ahmadalkawasmeh/HydraSmart/application preview/ecPage.png

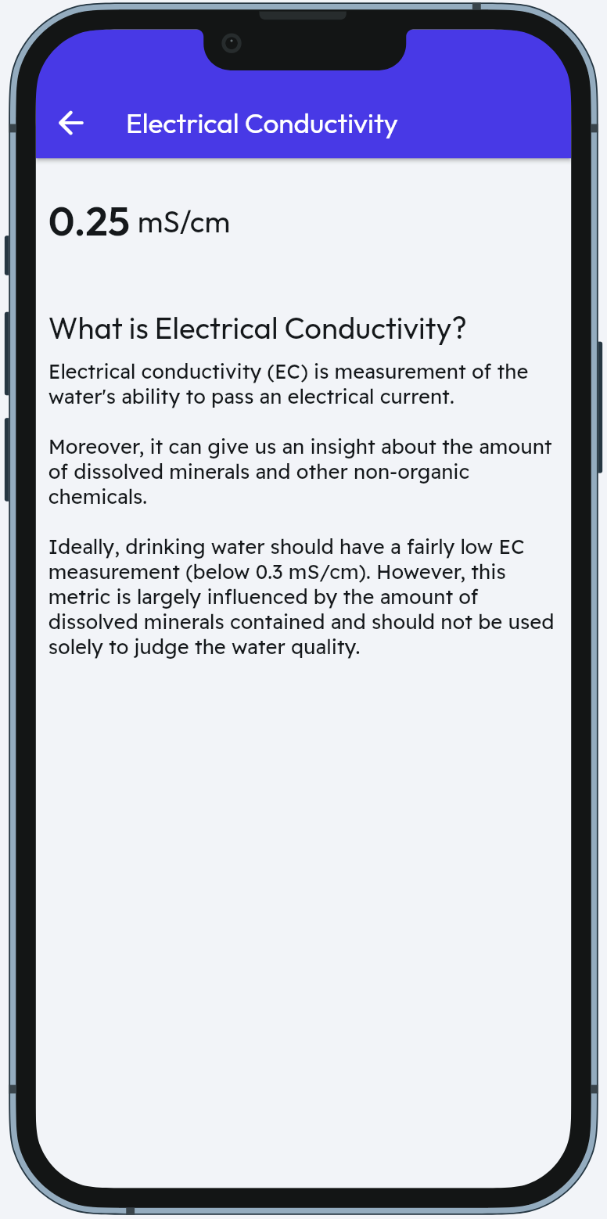
application preview/ecPage.png
