ahmadalkawasmeh/HydraSmart/application preview/homePage.png

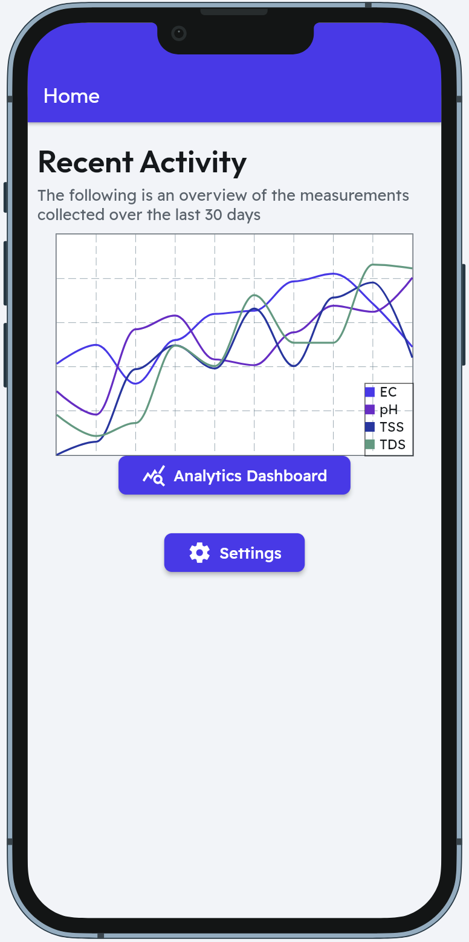
application preview/homePage.png
