ahmadalkawasmeh/HydraSmart/application preview/tdsPage.png

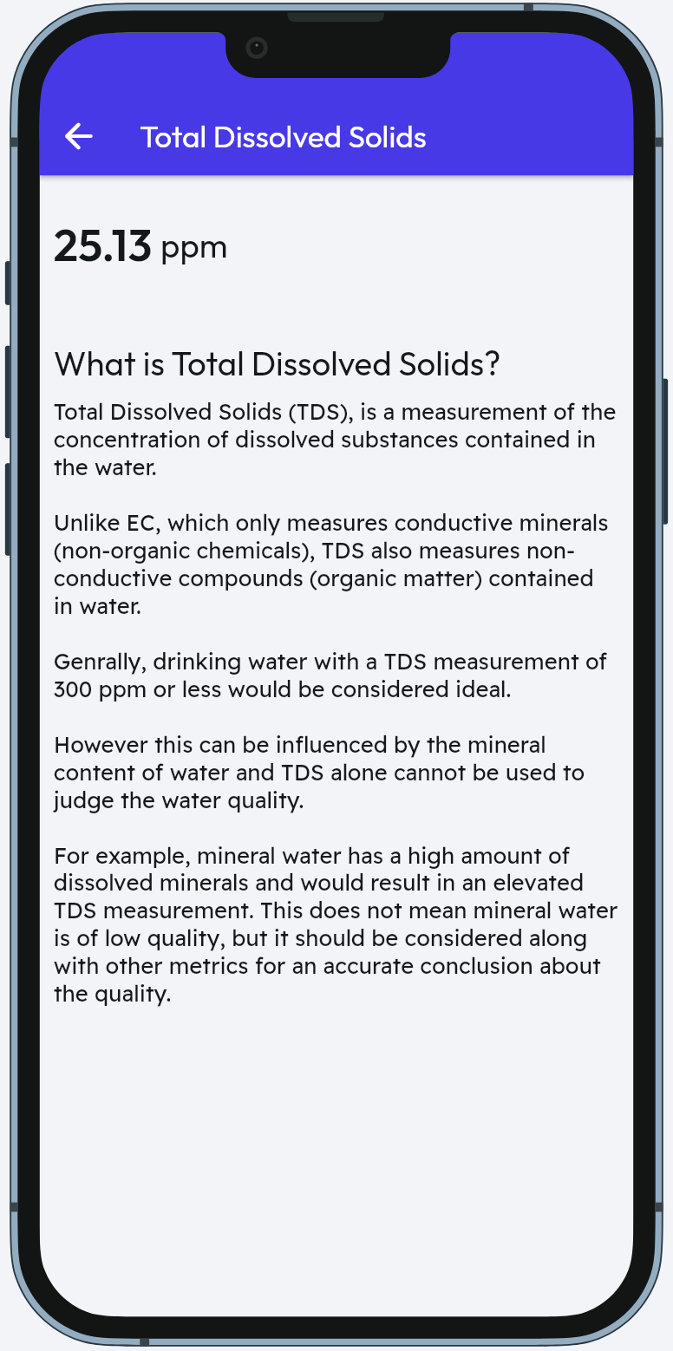
application preview/tdsPage.png
