ahmadalkawasmeh/HydraSmart/application preview/welcomePage.png

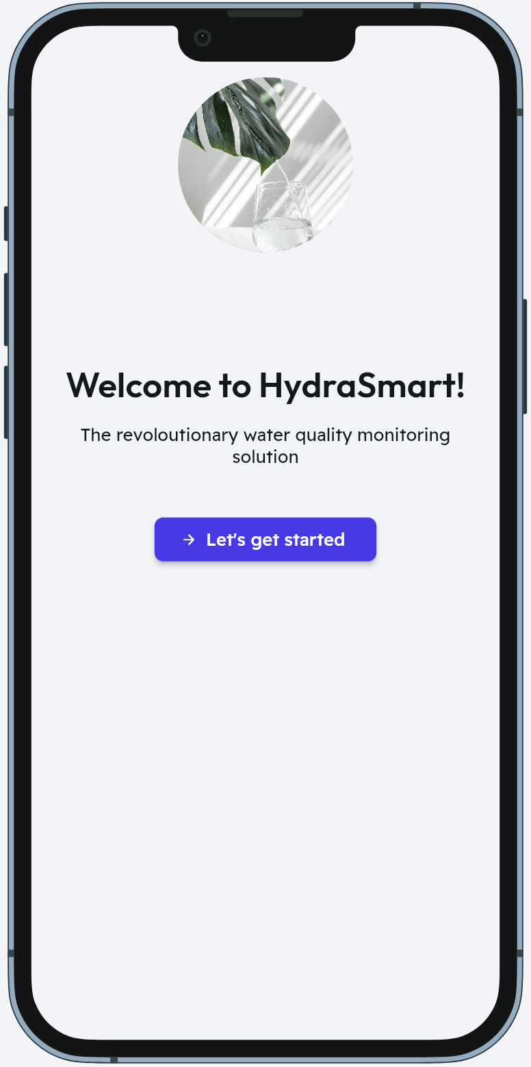
application preview/welcomePage.png
