ahmadalkawasmeh/HydraSmart/3D bottle design/Parts Renders/innerCylinderHousing.jpeg

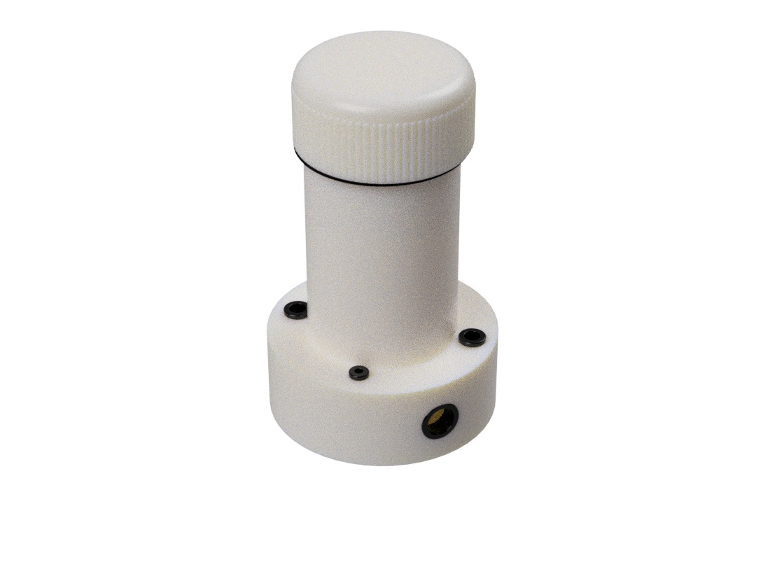
3D bottle design/Parts Renders/innerCylinderHousing.jpeg
