ahmadalkawasmeh/HydraSmart/3D bottle design/Parts STL/Grommet-3-TPU.stl

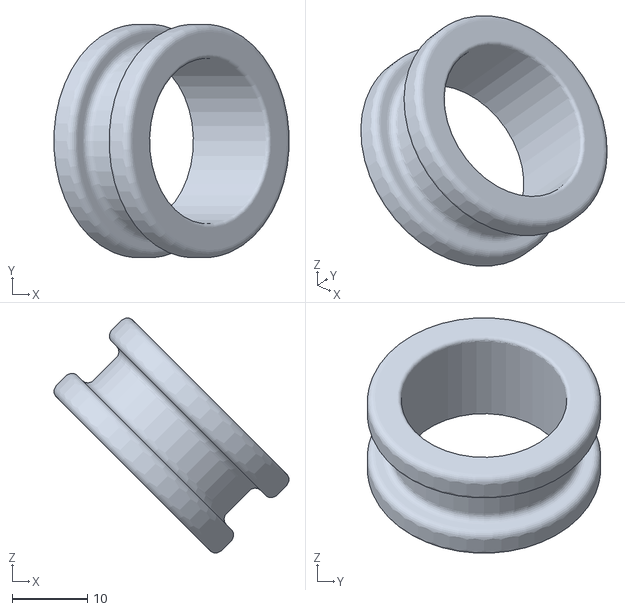
[picture p51: CAD file, 2024-07-06]
3D bottle design/Parts STL/Grommet-3-TPU.stl
31.2 x 31.0 x 31.2
